GilesMetcalf/eHarp/schematics/eHarp_schematics_MIDIboard.kicad_sch

## KiCad design schematics/eHarp_schematics_MIDIboard.kicad_sch (2026-06-29)

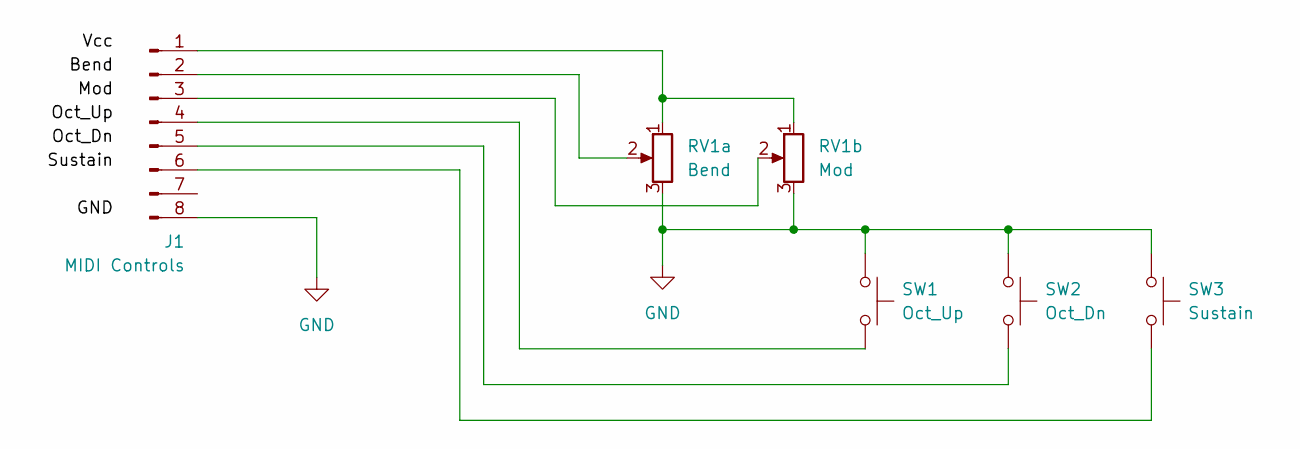
[picture p9: schematic eHarp_schematics_MIDIboard.kicad_sch]

Parts:
J1: MIDI Controls
RV1a: Bend
RV1b: Mod
SW1: Oct_Up
SW2: Oct_Dn
SW3: Sustain

Connections:
unnamed: J1.1, RV1a.1, RV1b.1
unnamed: J1.2, RV1a.2
unnamed: J1.3, RV1b.2
unnamed: J1.4, SW1.2
unnamed: J1.5, SW2.2
unnamed: J1.6, SW3.2
unnamed: RV1a.3, RV1b.3, SW1.1, SW2.1, SW3.1
