GilesMetcalf/eHarp/schematics/eHarp_schematics_displayboard.kicad_sch

## KiCad design schematics/eHarp_schematics_displayboard.kicad_sch (2026-06-29)

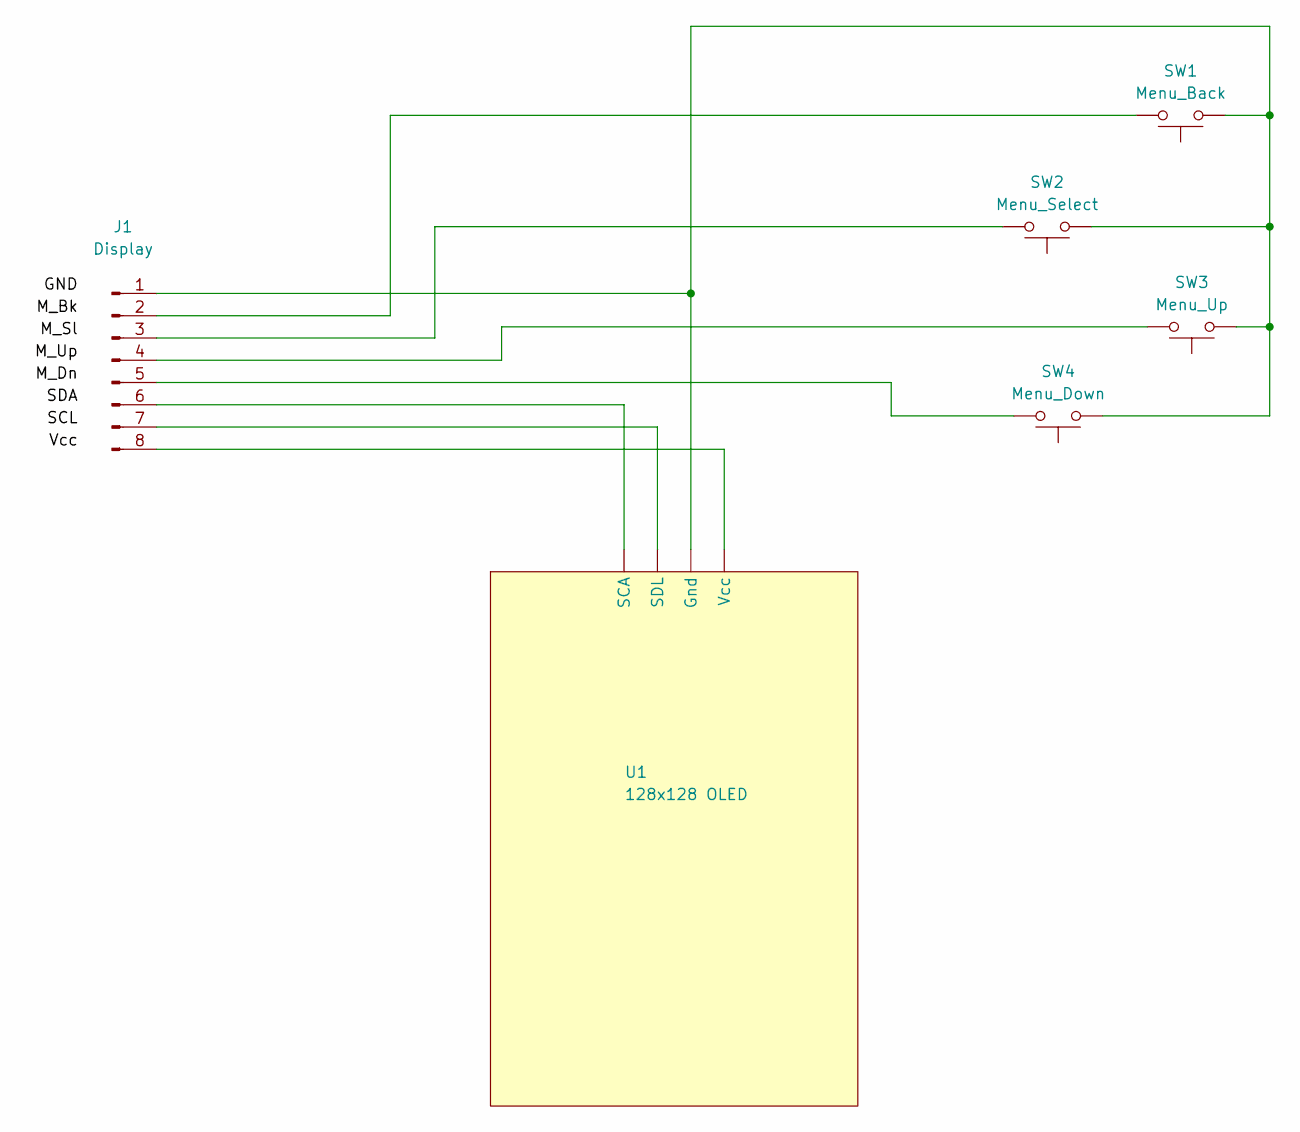
[picture p10: schematic eHarp_schematics_displayboard.kicad_sch]

Parts:
J1: Display
SW1: Menu_Back
SW2: Menu_Select
SW3: Menu_Up
SW4: Menu_Down
U1: 128x128 OLED

Connections:
unnamed: J1.1, SW1.2, SW2.2, SW3.2, SW4.2, U1.
unnamed: J1.2, SW1.1
unnamed: J1.3, SW2.1
unnamed: J1.4, SW3.1
unnamed: J1.5, SW4.1
unnamed: J1.6, U1.
unnamed: J1.7, U1.
unnamed: J1.8, U1.
