GilesMetcalf/eHarp/schematics/eHarp_sschematics_mainboard.kicad_sch

## KiCad design schematics/eHarp_sschematics_mainboard.kicad_sch (2026-06-24)

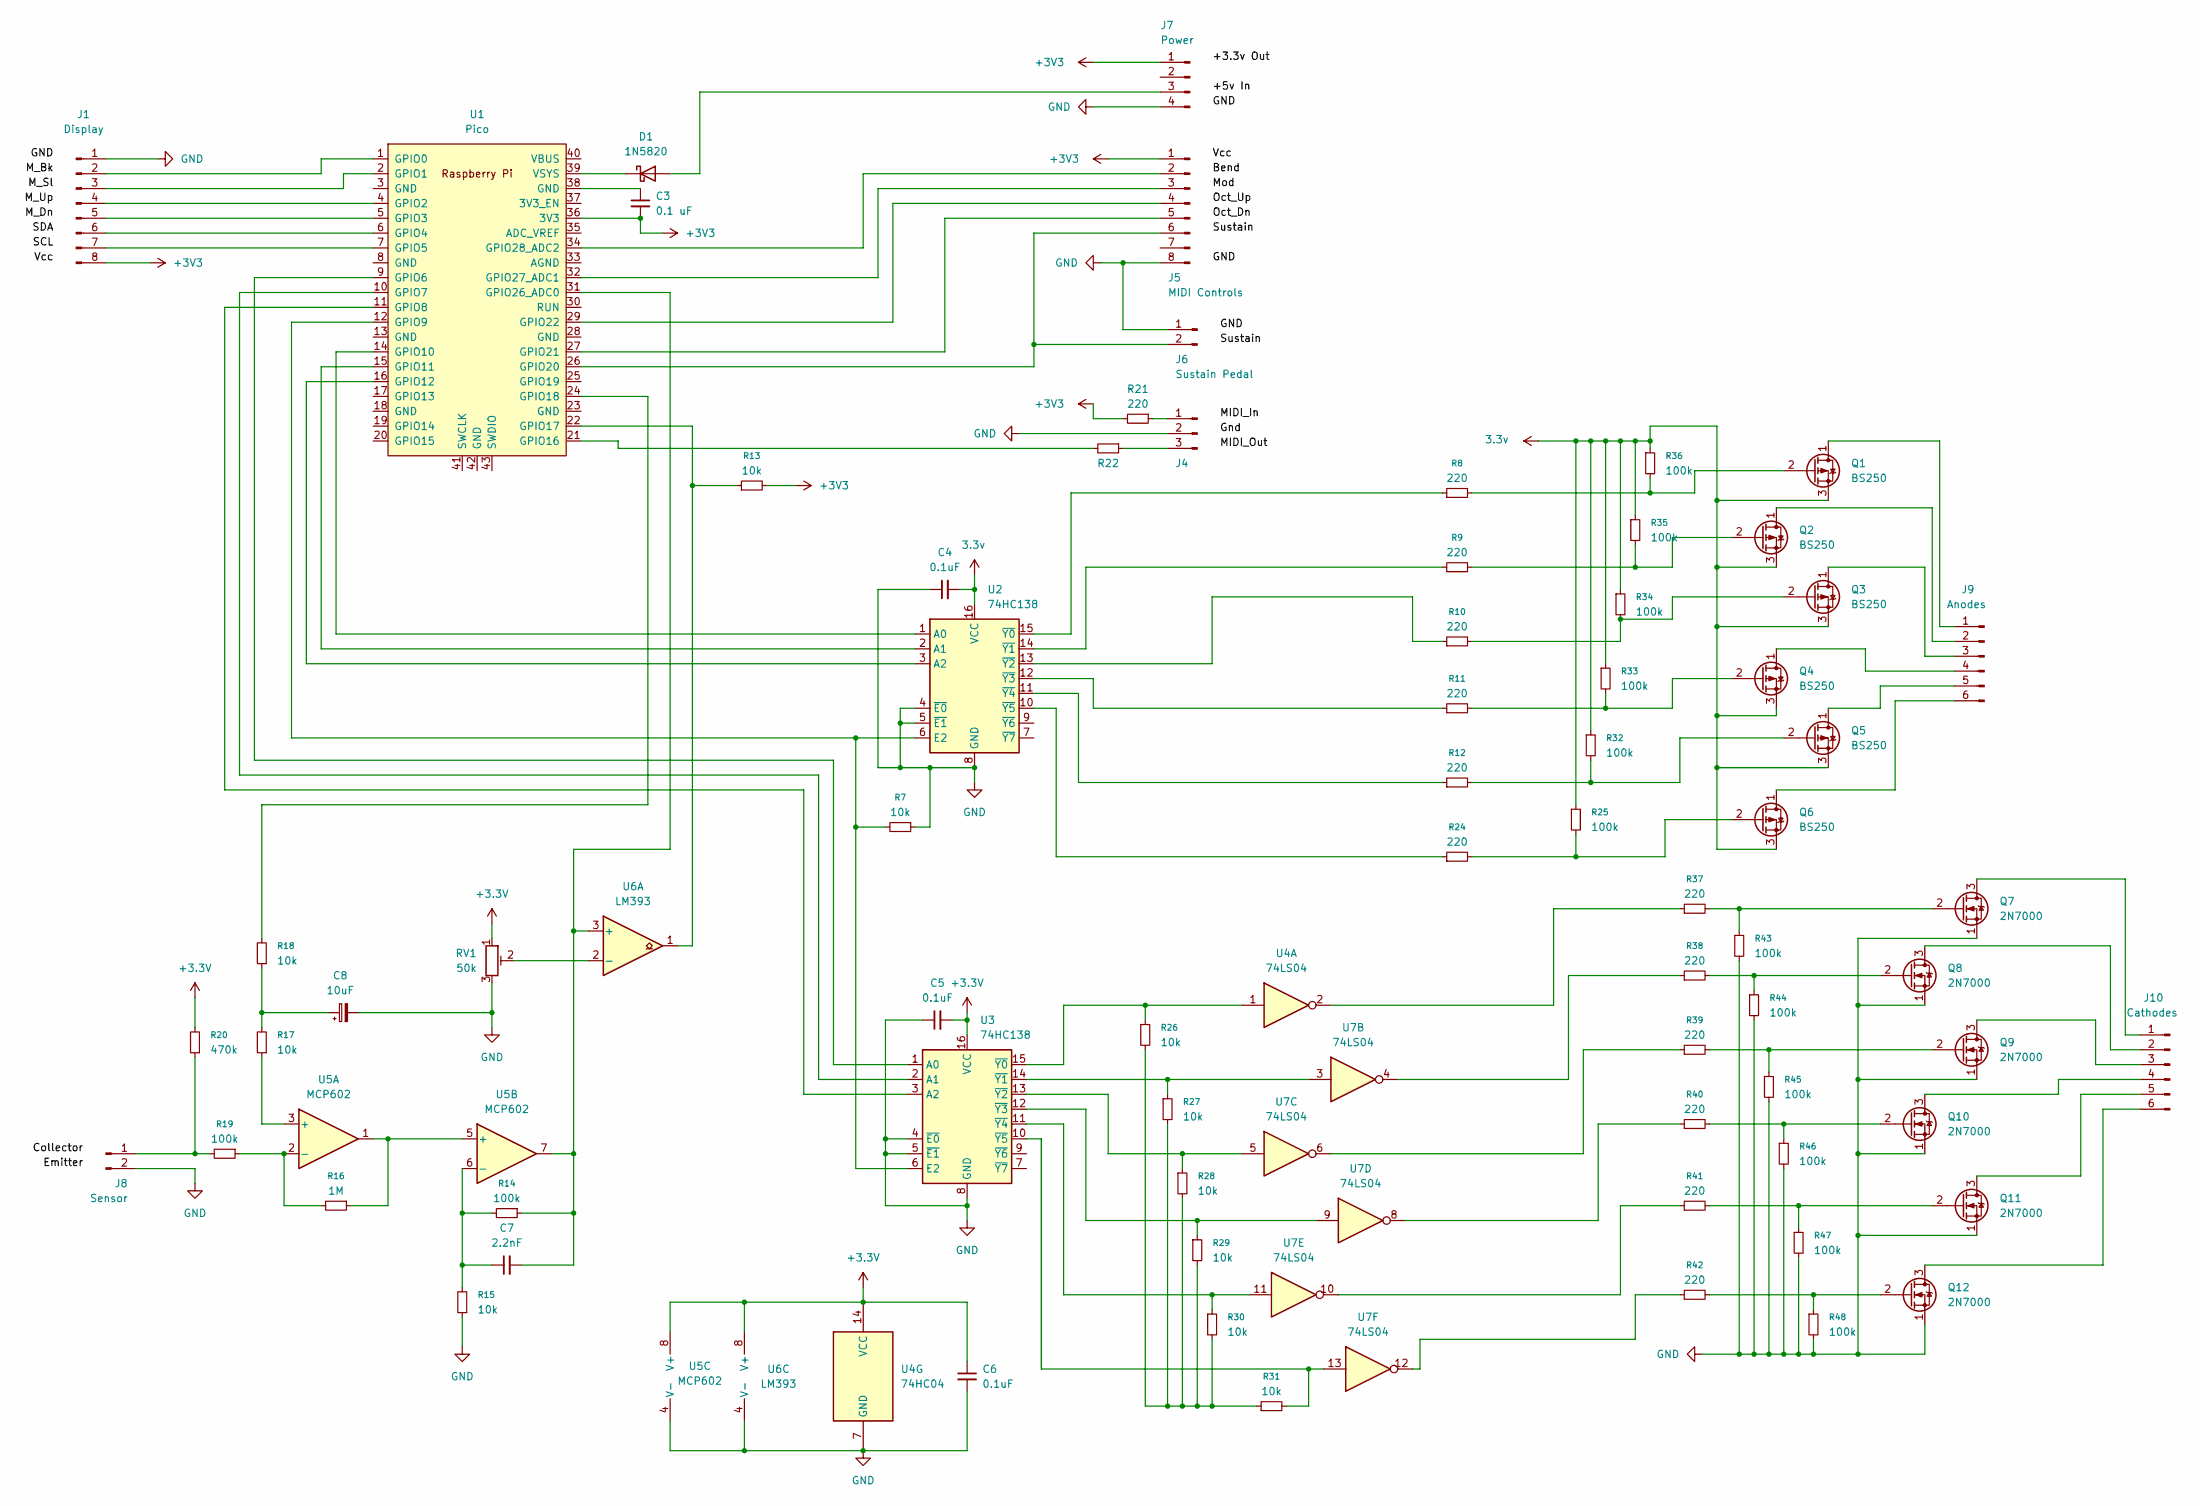
[picture p11: schematic eHarp_sschematics_mainboard.kicad_sch]

Parts:
C3: 0.1 uF; C_Rect_L9.0mm_W2.5mm_P7.50mm_MKT
C4, C5, C6: 0.1uF; C_Rect_L10.0mm_W3.0mm_P7.50mm_FKS3_FKP3
C7: 2.2nF; C_Rect_L10.0mm_W3.0mm_P7.50mm_FKS3_FKP3
C8: 10uF; CP_Radial_D10.0mm_P2.50mm
D1: 1N5820; D_DO-15_P10.16mm_Horizontal
J1: Display; PinHeader_1x08_P2.54mm_Vertical
J4: MIDI Jack; PinHeader_1x03_P2.54mm_Vertical
J5: MIDI Controls; PinHeader_1x08_P2.54mm_Vertical
J6: Sustain Pedal; PinHeader_1x02_P2.54mm_Vertical
J7: Power; PinHeader_1x04_P2.54mm_Vertical
J8: Sensor; PinHeader_1x02_P2.54mm_Vertical
J9: Anodes; PinHeader_1x06_P2.54mm_Vertical
J10: Cathodes; PinHeader_1x06_P2.54mm_Vertical
Q1, Q2, Q3, Q4, Q5, Q6: BS250; TO-92_Inline
Q7, Q8, Q9, Q10, Q11, Q12: 2N7000; TO-92_Inline
R7, R13, R15, R17, R18, R26, R27, R28, R29, R30, R31: 10k; R_Axial_DIN0204_L3.6mm_D1.6mm_P7.62mm_Horizontal
R8, R9, R10, R11, R12, R21, R22, R24, R37, R38, R39, R40, R41, R42: 220; R_Axial_DIN0204_L3.6mm_D1.6mm_P7.62mm_Horizontal
R14, R19, R25, R32, R33, R34, R35, R36, R43, R44, R45, R46, R47, R48: 100k; R_Axial_DIN0204_L3.6mm_D1.6mm_P7.62mm_Horizontal
R16: 1M; R_Axial_DIN0204_L3.6mm_D1.6mm_P7.62mm_Horizontal
R20: 470k; R_Axial_DIN0204_L3.6mm_D1.6mm_P7.62mm_Horizontal
RV1: 50k; Potentiometer_Vishay_T93YA_Vertical
U1: Pico; DIP-40_W25.4mm_Socket
U2, U3: 74HC138; DIP-16_W10.16mm
U4: 74HC04; DIP-14_W7.62mm
U5: MCP602; CERDIP-8_W7.62mm_SideBrazed
U6: LM393; CERDIP-8_W7.62mm_SideBrazed
U7: 74LS04; DIP-14_W7.62mm

Connections:
3.3v: C4.2, Q1.3 (S), Q2.3 (S), Q3.3 (S), Q4.3 (S), Q5.3 (S), Q6.3 (S), R25.1, R32.1, R33.1, R34.1, R35.1, R36.1, U2.16 (VCC)
+3.3V: C5.2, C6.1, R20.2, RV1.1, U3.16 (VCC), U4.14 (VCC), U5.8 (V+), U6.8 (V+)
+3V3: C3.2, J1.8, J5.1, J7.1, R13.2, R21.2, U1.36 (3V3)
GND: C4.1, C5.1, C6.2, C8.2, J1.1, J4.2, J5.8, J6.1, J7.4, J8.2, Q7.1 (S), Q8.1 (S), Q9.1 (S), Q10.1 (S), Q11.1 (S), Q12.1 (S), R7.1, R15.1, R43.2, R44.2, R45.2, R46.2, R47.2, R48.2, RV1.3, U2.4 (~E0), U2.5 (~E1), U2.8 (GND), U3.4 (~E0), U3.5 (~E1), U3.8 (GND), U4.7 (GND), U5.4 (V-), U6.4 (V-)
unnamed: C3.1, U1.38 (GND)
unnamed: C7.1, R14.2, R15.2, U5.6 (-)
unnamed: C7.2, R14.1, U1.31 (GPIO26_ADC0), U5.7, U6.3 (+)
unnamed: C8.1, R17.2, R18.1
unnamed: D1.1 (K), U1.39 (VSYS)
unnamed: D1.2 (A), J7.3
unnamed: J1.2, U1.1 (GPIO0)
unnamed: J1.3, U1.2 (GPIO1)
unnamed: J1.4, U1.4 (GPIO2)
unnamed: J1.5, U1.5 (GPIO3)
unnamed: J1.6, U1.6 (GPIO4)
unnamed: J1.7, U1.7 (GPIO5)
unnamed: J4.1, R21.1
unnamed: J4.3, R22.1
unnamed: J5.2, U1.34 (GPIO28_ADC2)
unnamed: J5.3, U1.32 (GPIO27_ADC1)
unnamed: J5.4, U1.29 (GPIO22)
unnamed: J5.5, U1.27 (GPIO21)
unnamed: J5.6, J6.2, U1.26 (GPIO20)
unnamed: J8.1, R19.2, R20.1
unnamed: J9.1, Q1.1 (D)
unnamed: J9.2, Q2.1 (D)
unnamed: J9.3, Q3.1 (D)
unnamed: J9.4, Q4.1 (D)
unnamed: J9.5, Q5.1 (D)
unnamed: J9.6, Q6.1 (D)
unnamed: J10.1, Q7.3 (D)
unnamed: J10.2, Q8.3 (D)
unnamed: J10.3, Q9.3 (D)
unnamed: J10.4, Q10.3 (D)
unnamed: J10.5, Q11.3 (D)
unnamed: J10.6, Q12.3 (D)
unnamed: Q1.2 (G), R8.2, R36.2
unnamed: Q2.2 (G), R9.2, R35.2
unnamed: Q3.2 (G), R10.2, R34.2
unnamed: Q4.2 (G), R11.2, R33.2
unnamed: Q5.2 (G), R12.2, R32.2
unnamed: Q6.2 (G), R24.2, R25.2
unnamed: Q7.2 (G), R37.2, R43.1
unnamed: Q8.2 (G), R38.2, R44.1
unnamed: Q9.2 (G), R39.2, R45.1
unnamed: Q10.2 (G), R40.2, R46.1
unnamed: Q11.2 (G), R41.2, R47.1
unnamed: Q12.2 (G), R42.2, R48.1
unnamed: R7.2, U1.12 (GPIO9), U2.6 (E2), U3.6 (E2)
unnamed: R8.1, U2.15 (~Y0)
unnamed: R9.1, U2.14 (~Y1)
unnamed: R10.1, U2.13 (~Y2)
unnamed: R11.1, U2.12 (~Y3)
unnamed: R12.1, U2.11 (~Y4)
unnamed: R13.1, U1.22 (GPIO17), U6.1
unnamed: R16.1, U5.1, U5.5 (+)
unnamed: R16.2, R19.1, U5.2 (-)
unnamed: R17.1, U5.3 (+)
unnamed: R18.2, U1.24 (GPIO18)
unnamed: R22.2, U1.21 (GPIO16)
unnamed: R24.1, U2.10 (~Y5)
unnamed: R26.1, U3.15 (~Y0), U4.1
unnamed: R26.2, R27.2, R28.2, R29.2, R30.2, R31.1
unnamed: R27.1, U3.14 (~Y1), U7.3
unnamed: R28.1, U3.13 (~Y2), U7.5
unnamed: R29.1, U3.12 (~Y3), U7.9
unnamed: R30.1, U3.11 (~Y4), U7.11
unnamed: R31.2, U3.10 (~Y5), U7.13
unnamed: R37.1, U4.2
unnamed: R38.1, U7.4
unnamed: R39.1, U7.6
unnamed: R40.1, U7.8
unnamed: R41.1, U7.10
unnamed: R42.1, U7.12
unnamed: RV1.2, U6.2 (-)
unnamed: U1.9 (GPIO6), U3.1 (A0)
unnamed: U1.10 (GPIO7), U3.2 (A1)
unnamed: U1.11 (GPIO8), U3.3 (A2)
unnamed: U1.14 (GPIO10), U2.1 (A0)
unnamed: U1.15 (GPIO11), U2.2 (A1)
unnamed: U1.16 (GPIO12), U2.3 (A2)
